RavensWurk/MacJukebox/Board/Drivers/UartInterface/uart_interface.c

#include "uart_interface.h"

#define MAX_CALLBACKS 10

void (*callbacks[MAX_CALLBACKS])(Command*);

// Temporary storage for incoming commands
char uart_data[256];
size_t current_len;

void UartInterface_Received(uint8_t data)
{
    uart_data[current_len++] = data;

    Command command = Command_init_zero;

    if (Command_search(uart_data, current_len, &command))
    {
        for (int i=0;i<MAX_CALLBACKS;i++)
        {
            if (callbacks[i] != NULL)
            {
                callbacks[i](&command);
            }
        }
        current_len = 0;

    }
    else if (current_len == sizeof (uart_data) - 1)
    {
        current_len = 0;
    }
}

void UartInterface_Init(UART_HandleTypeDef *uart)
{
    __HAL_UART_ENABLE_IT(uart, UART_IT_RXNE);
}

void UartInterface_OnCommand(void (*callback)(Command*))
{
    for (int i=0;i<MAX_CALLBACKS;i++)
    {
        if (callbacks[i] == NULL)
        {
            callbacks[i] = callback;
            return;
        }
    }
}

void UartInterface_Write(UART_HandleTypeDef *uart, const void* data, size_t len)
{
    HAL_UART_Transmit(uart, (uint8_t*)data, len, 10000);
}
